Jacob-Hocevar/red-avi-tamu/Elysium/GIGAPCB/GIGAPCB KiCAD Library/3D Models/CONN_5-2301995-2_RJ45.stp

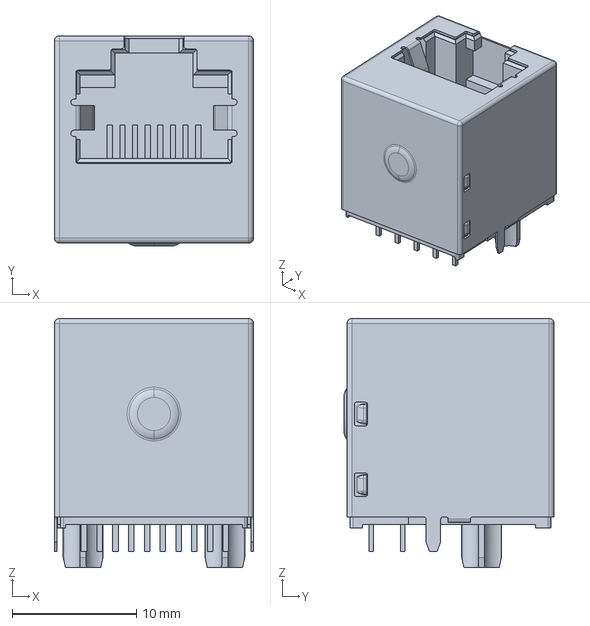
[picture p15: CAD file, 2025-02-18]
Elysium/GIGAPCB/GIGAPCB KiCAD Library/3D Models/CONN_5-2301995-2_RJ45.stp
16.1 x 16.9 x 20.1 mm
