Jacob-Hocevar/red-avi-tamu/Elysium/GIGAPCB/GIGAPCB KiCAD Library/3D Models/C_KRM55WR72A226MH01L.step

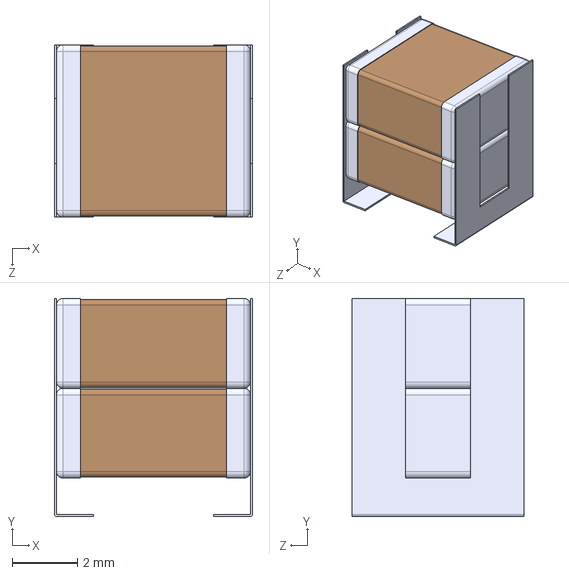
[picture p16: CAD file, 2025-02-18]
Elysium/GIGAPCB/GIGAPCB KiCAD Library/3D Models/C_KRM55WR72A226MH01L.step
6.10 x 6.70 x 5.30 mm
