Jacob-Hocevar/red-avi-tamu/Elysium/GIGAPCB/GIGAPCB KiCAD Library/3D Models/CP_UCS2C331MHD.step

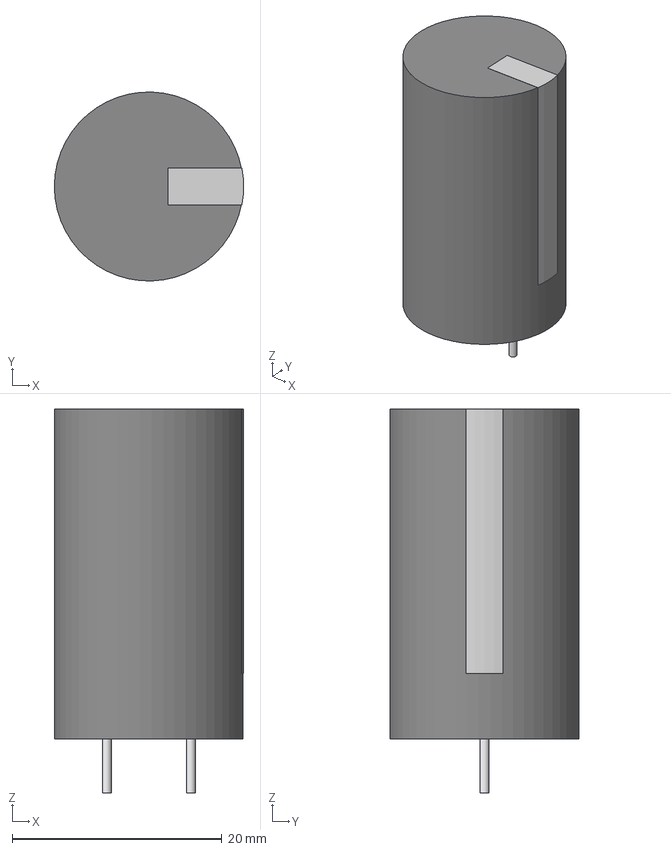
[picture p17: CAD file, 2025-02-18]
Elysium/GIGAPCB/GIGAPCB KiCAD Library/3D Models/CP_UCS2C331MHD.step
18.0 x 18.0 x 36.6 mm
