Jacob-Hocevar/red-avi-tamu/Elysium/GIGAPCB/GIGAPCB KiCAD Library/3D Models/DCC_I7C4W012A050V-003-R.step

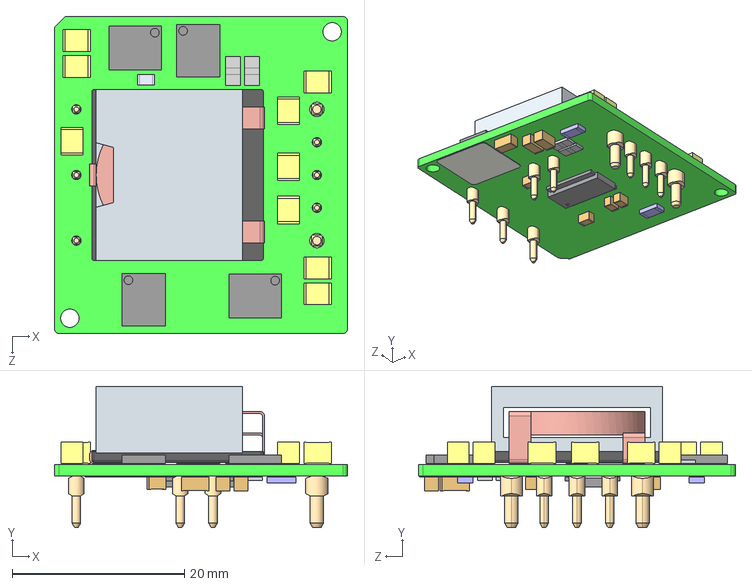
[picture p18: CAD file, 2025-02-18]
Elysium/GIGAPCB/GIGAPCB KiCAD Library/3D Models/DCC_I7C4W012A050V-003-R.step
34.0 x 16.4 x 36.8 mm
