Jacob-Hocevar/red-avi-tamu/Elysium/GIGAPCB/GIGAPCB KiCAD Library/3D Models/CONN_1722981104_Universal.step

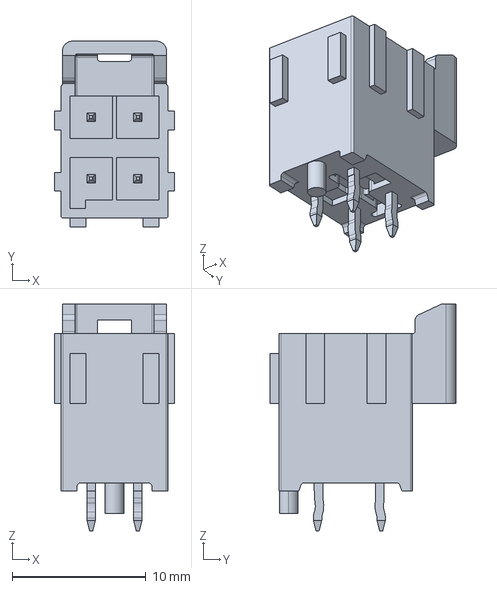
[picture p19: CAD file, 2025-02-18]
Elysium/GIGAPCB/GIGAPCB KiCAD Library/3D Models/CONN_1722981104_Universal.step
9.00 x 13.9 x 17.0 mm
