Jacob-Hocevar/red-avi-tamu/Elysium/GIGAPCB/GIGAPCB KiCAD Library/3D Models/CP_UCZ2A301MNQ1MS.step

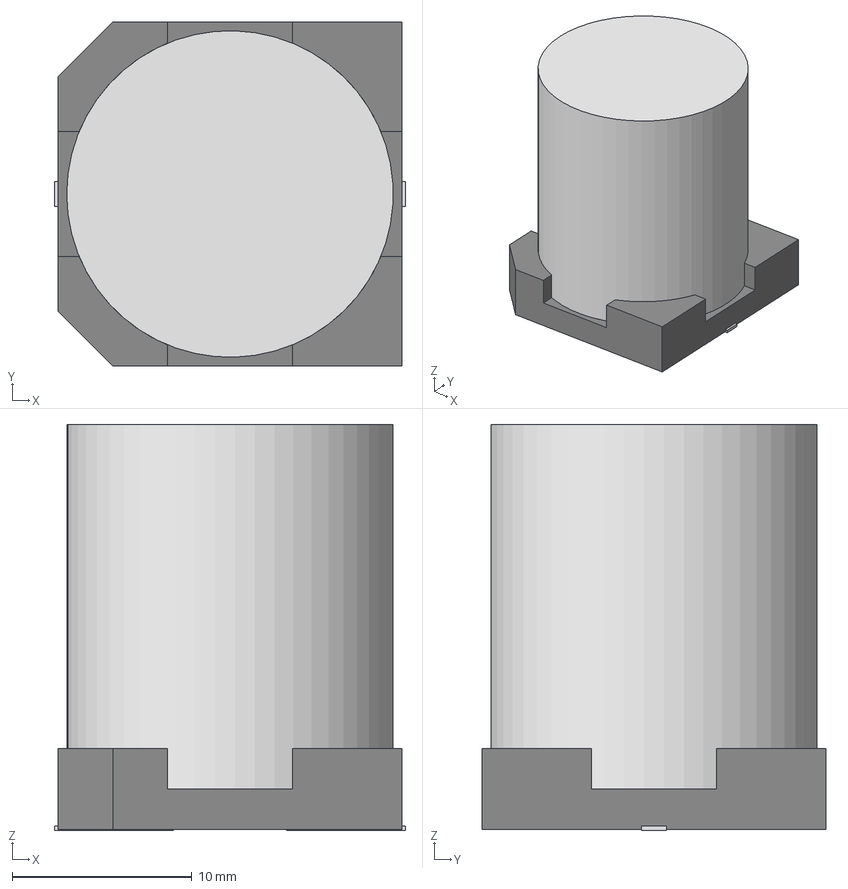
[picture p20: CAD file, 2025-02-18]
Elysium/GIGAPCB/GIGAPCB KiCAD Library/3D Models/CP_UCZ2A301MNQ1MS.step
19.5 x 19.1 x 22.6 mm
