Jacob-Hocevar/red-avi-tamu/Elysium/GIGAPCB/GIGAPCB KiCAD Library/3D Models/CP_UBY1K471MHL.step

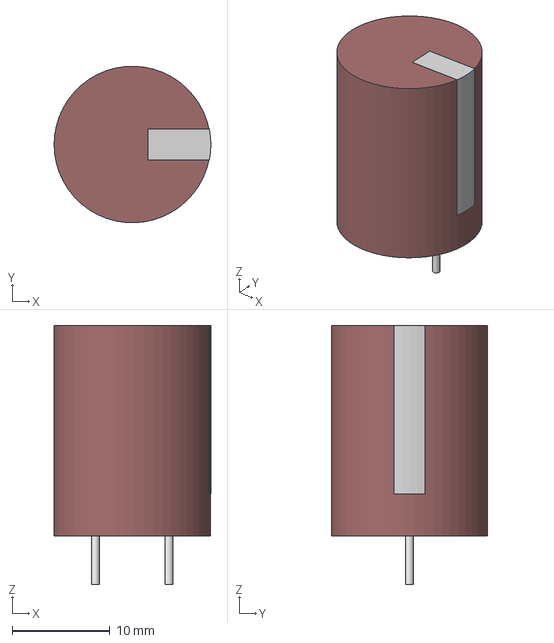
[picture p21: CAD file, 2025-02-18]
Elysium/GIGAPCB/GIGAPCB KiCAD Library/3D Models/CP_UBY1K471MHL.step
16.0 x 16.0 x 26.5 mm
