Jacob-Hocevar/red-avi-tamu/Elysium/GIGAPCB/GIGAPCB KiCAD Library/3D Models/CONN_2601_3110.stp

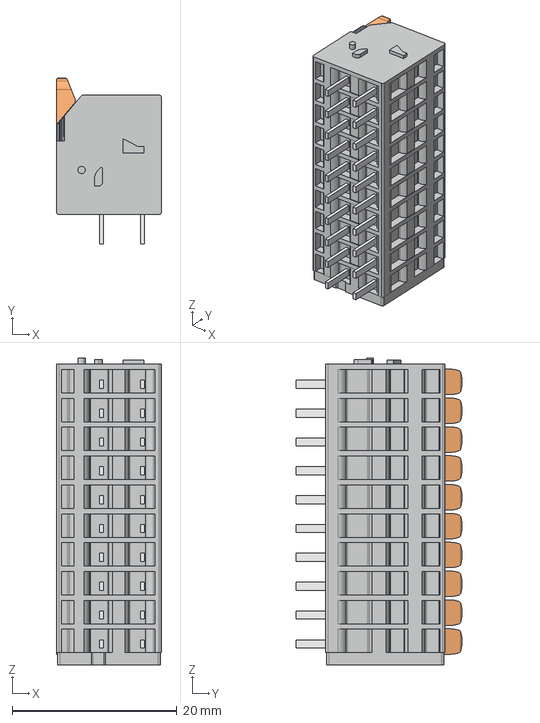
[picture p22: CAD file, 2025-02-18]
Elysium/GIGAPCB/GIGAPCB KiCAD Library/3D Models/CONN_2601_3110.stp
12.8 x 20.2 x 37.2 mm
