Jacob-Hocevar/red-avi-tamu/Elysium/GIGAPCB/GIGAPCB KiCAD Library/3D Models/CONN_1722981108_Universal.stp

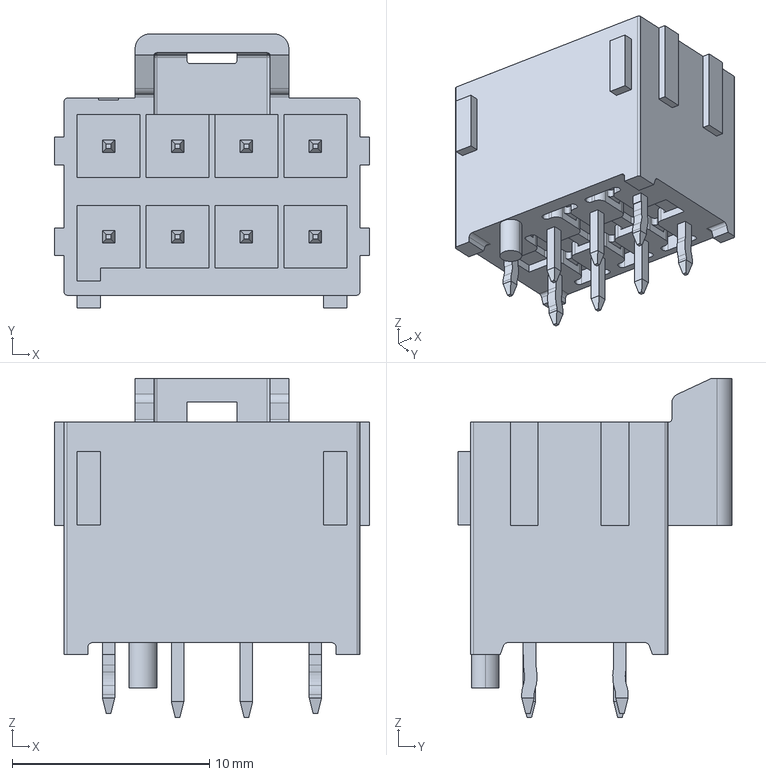
[picture p23: CAD file, 2025-02-18]
Elysium/GIGAPCB/GIGAPCB KiCAD Library/3D Models/CONN_1722981108_Universal.stp
16.0 x 13.9 x 17.2 mm
