Jacob-Hocevar/red-avi-tamu/Elysium/GIGAPCB/GIGAPCB KiCAD Library/3D Models/IC_TCA9548APWR.stp

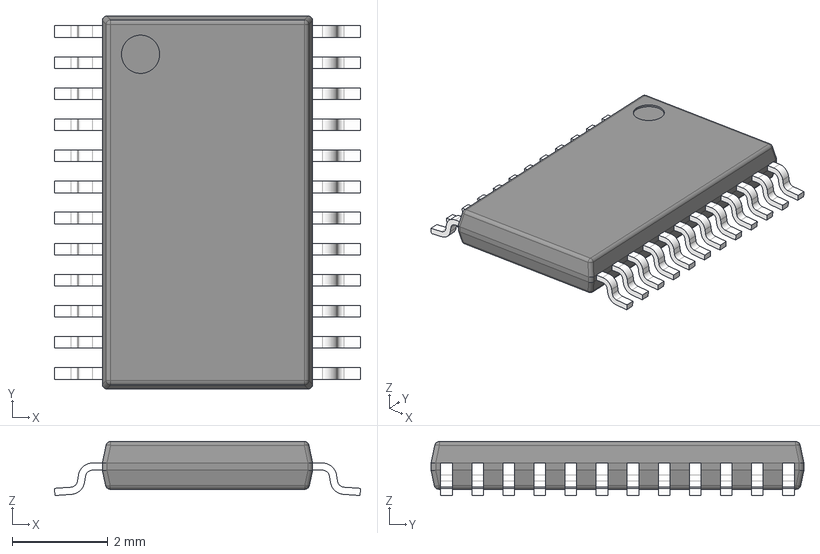
[picture p24: CAD file, 2025-02-18]
Elysium/GIGAPCB/GIGAPCB KiCAD Library/3D Models/IC_TCA9548APWR.stp
6.40 x 7.80 x 1.13 mm
BODY-TSSOP
LEAD-TSSOP x 24
PIN1
