Jacob-Hocevar/red-avi-tamu/Elysium/Real_Teensy/Elysium_teensy/IMU.h

#ifndef GUARD_IMU
#define GUARD_IMU

void detectIMU();
void enableIMU();
void readACC(byte buff[]);
void readMAG(byte buff[]);
void readGYR(byte buff[]);


void writeTo(int device, byte address, byte val);
void readFrom(int device, byte address, int num, byte buff[]);

#endif
