Jacob-Hocevar/red-avi-tamu/Elysium/Elysium_GUI/Sources/Standard_Label.cpp

#include "Standard_Label.h"
#include <Qt>

Standard_Label::Standard_Label(const QString& text, QGridLayout* layout, int row): QLabel() {
    this->setText(text);
    this->setAlignment(Qt::AlignLeft | Qt::AlignVCenter);
    layout->addWidget(this, row, 0);
}
